V0v1kkk/GraduationProject/Images/1.png

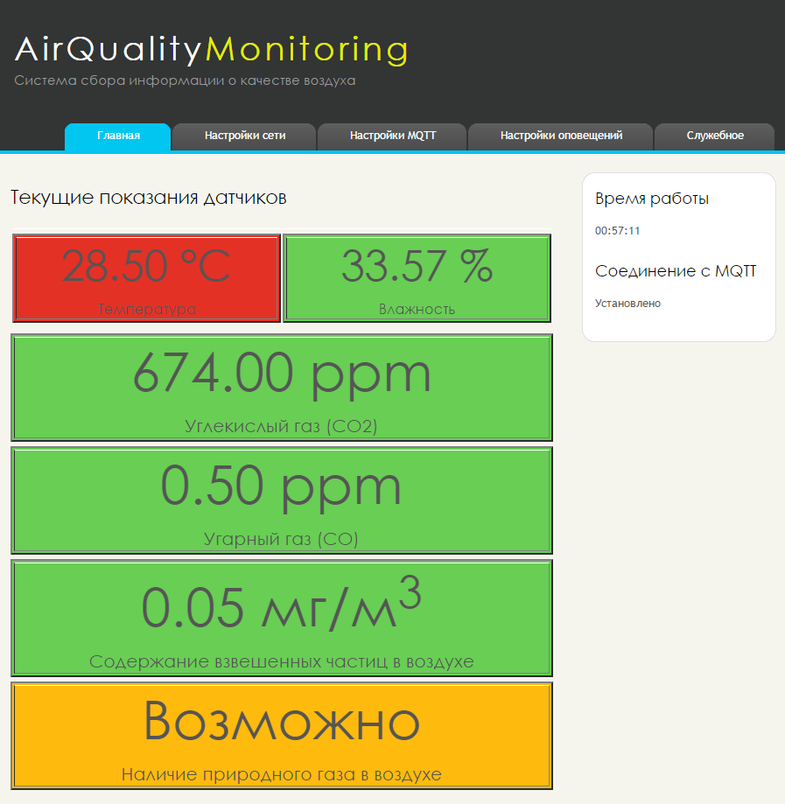
Images/1.png
