V0v1kkk/GraduationProject/Images/2.png

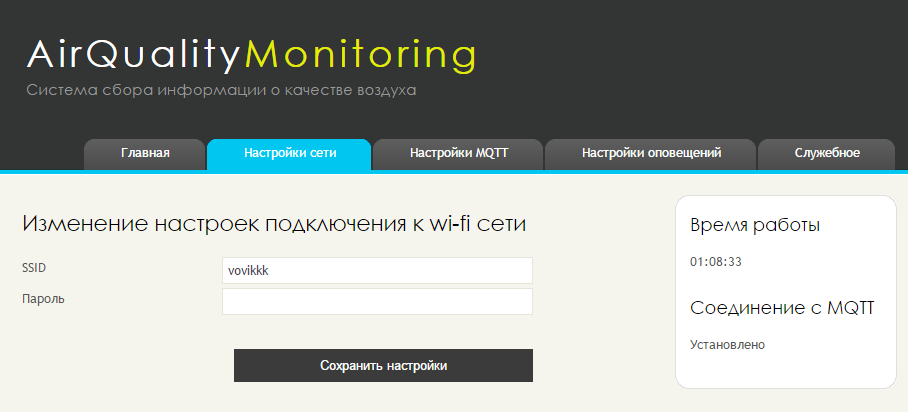
Images/2.png
