V0v1kkk/GraduationProject/Images/3.png

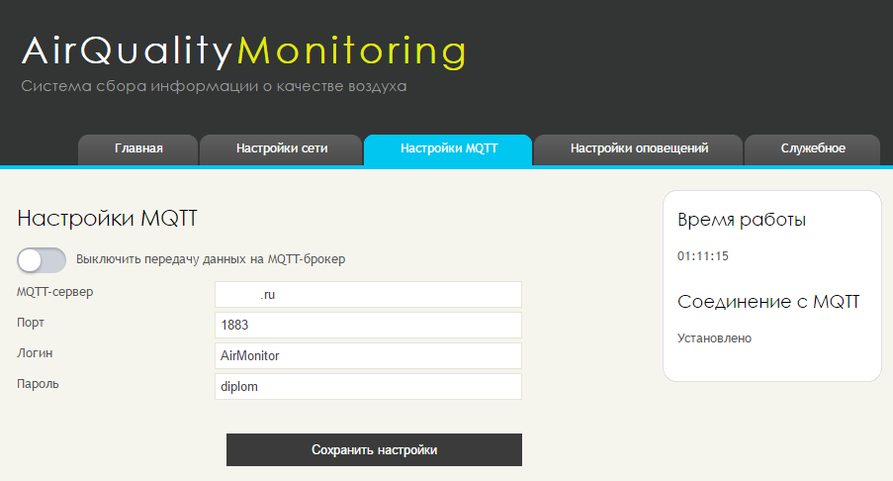
Images/3.png
