V0v1kkk/GraduationProject/Images/4.png

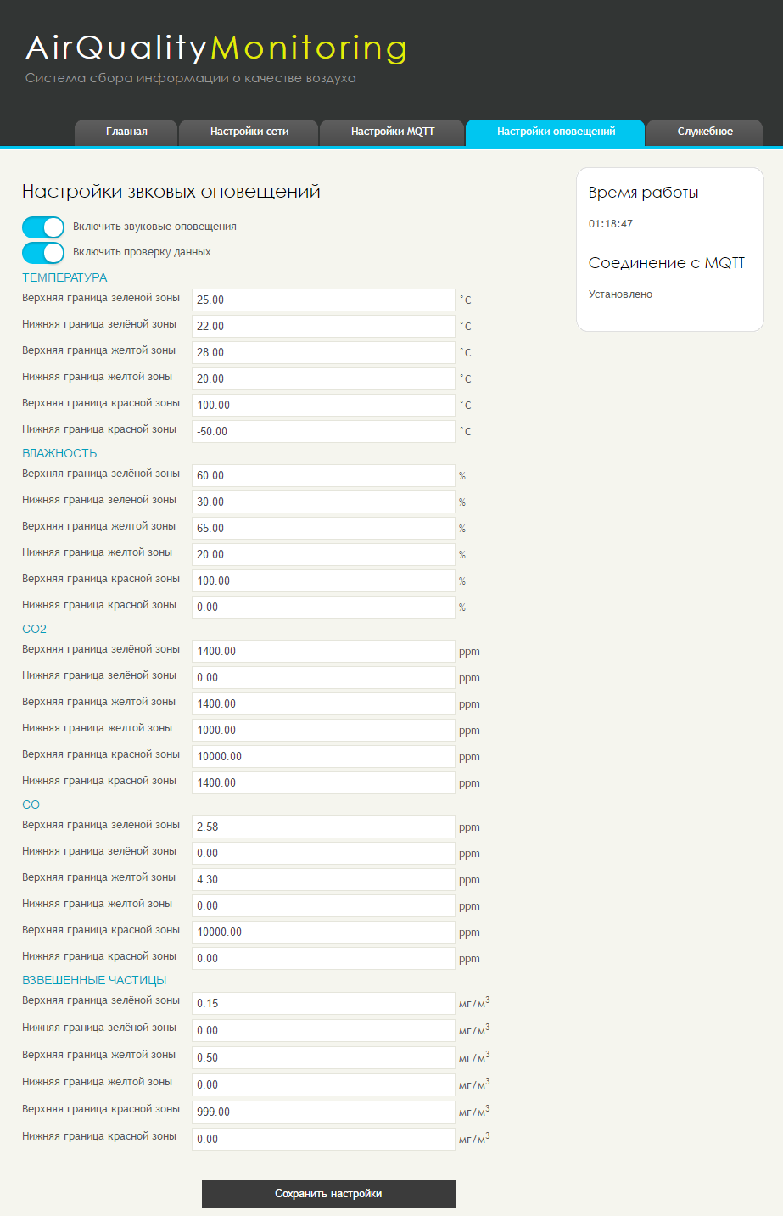
Images/4.png
