V0v1kkk/GraduationProject/Images/5.png

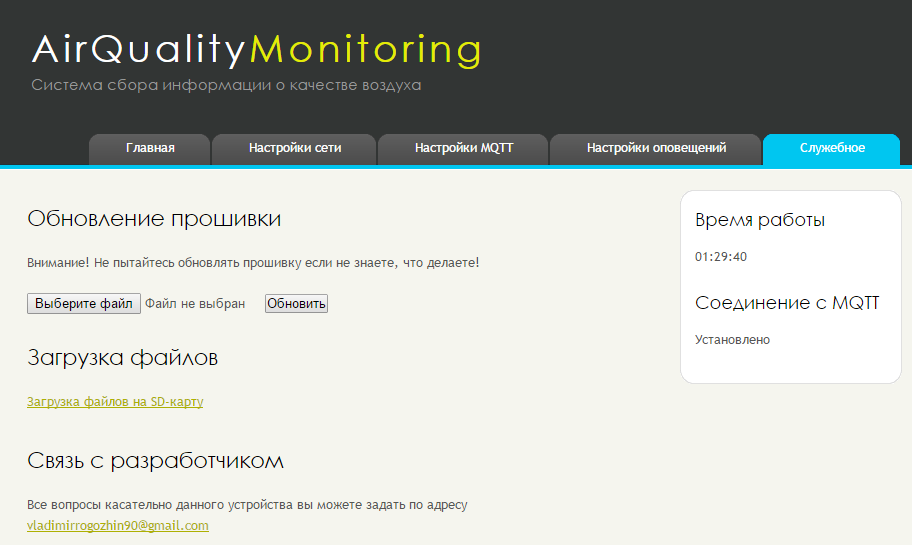
Images/5.png
